Tinkerforge/can-v2-bricklet/software/src/tfcan_mo.c

/* can-v2-bricklet
 * Copyright (C) 2018 Matthias Bolte <matthias@tinkerforge.com>
 *
 * tfcan_mo.c: XMC CAN Message Object helpers
 *
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
 * You should have received a copy of the GNU Lesser General Public
 * License along with this library; if not, write to the
 * Free Software Foundation, Inc., 59 Temple Place - Suite 330,
 * Boston, MA 02111-1307, USA.
 */

#include "tfcan_mo.h"

#include "configs/config.h"
#include "configs/config_tfcan.h"
#include "bricklib2/logging/logging.h"

#include "xmc_can.h"
#include "xmc_can_map.h"

void tfcan_mo_init_tx(CAN_MO_TypeDef *const mo) {
	// reset all status bits
	tfcan_mo_change_status(mo, TFCAN_MO_RESET_STATUS_RX_PENDING |
	                           TFCAN_MO_RESET_STATUS_TX_PENDING |
	                           TFCAN_MO_RESET_STATUS_RX_UPDATING |
	                           TFCAN_MO_RESET_STATUS_NEW_DATA |
	                           TFCAN_MO_RESET_STATUS_MESSAGE_LOST |
	                           TFCAN_MO_RESET_STATUS_MESSAGE_VALID |
	                           TFCAN_MO_RESET_STATUS_RX_TX_SELECTED |
	                           TFCAN_MO_RESET_STATUS_RX_ENABLE |
	                           TFCAN_MO_RESET_STATUS_TX_REQUEST |
	                           TFCAN_MO_RESET_STATUS_TX_ENABLE0 |
	                           TFCAN_MO_RESET_STATUS_TX_ENABLE1 |
	                           TFCAN_MO_RESET_STATUS_DIRECTION);

	// configure MPN and clear all other MOIPR parts
	mo->MOIPR = (((uint32_t)mo - CAN_BASE - 0x1000U) / 0x0020U) << CAN_MO_MOIPR_MPN_Pos;

	// reset all MOFCR parts
	mo->MOFCR = 0;

	// reset all MOFGPR parts
	mo->MOFGPR = 0;

	// reset all MOAMR parts
	mo->MOAMR = 0x3FFFFFFF;

	// clear idenfifier and set priority to 1
	mo->MOAR = 1U << CAN_MO_MOAR_PRI_Pos;

	// clear data
	mo->MODATAL = 0;
	mo->MODATAH = 0;

	// set direction to TX and mark as valid
	tfcan_mo_change_status(mo, TFCAN_MO_SET_STATUS_DIRECTION |
	                           TFCAN_MO_SET_STATUS_MESSAGE_VALID);
}

void tfcan_mo_init_tx_fifo_base(CAN_MO_TypeDef *const mo, const uint8_t base_and_bottom,
                                const uint8_t top) {
	mo->MOFCR = (mo->MOFCR & ~(uint32_t)CAN_MO_MOFCR_MMC_Msk) |
	            (((uint32_t)0x2u << CAN_MO_MOFCR_MMC_Pos) & (uint32_t)CAN_MO_MOFCR_MMC_Msk);

	mo->MOFGPR = (mo->MOFGPR & ~(uint32_t)(CAN_MO_MOFGPR_BOT_Msk |
	                                       CAN_MO_MOFGPR_TOP_Msk |
	                                       CAN_MO_MOFGPR_CUR_Msk)) |
	             (((uint32_t)base_and_bottom << CAN_MO_MOFGPR_CUR_Pos) & (uint32_t)CAN_MO_MOFGPR_CUR_Msk) |
	             (((uint32_t)top << CAN_MO_MOFGPR_TOP_Pos) & (uint32_t)CAN_MO_MOFGPR_TOP_Msk) |
	             (((uint32_t)base_and_bottom << CAN_MO_MOFGPR_BOT_Pos) & (uint32_t)CAN_MO_MOFGPR_BOT_Msk);

	tfcan_mo_change_status(mo, TFCAN_MO_SET_STATUS_TX_ENABLE0 |
	                           TFCAN_MO_SET_STATUS_TX_ENABLE1);
}

void tfcan_mo_init_tx_fifo_slave(CAN_MO_TypeDef *const mo, const uint8_t base) {
	mo->MOFCR = (mo->MOFCR & ~(uint32_t)CAN_MO_MOFCR_MMC_Msk) |
	            (((uint32_t)0x3u << CAN_MO_MOFCR_MMC_Pos) & (uint32_t)CAN_MO_MOFCR_MMC_Msk);

	mo->MOFGPR = (mo->MOFGPR & ~(uint32_t)(CAN_MO_MOFGPR_BOT_Msk |
	                                       CAN_MO_MOFGPR_TOP_Msk |
	                                       CAN_MO_MOFGPR_CUR_Msk)) |
	             (((uint32_t)base << CAN_MO_MOFGPR_CUR_Pos) & (uint32_t)CAN_MO_MOFGPR_CUR_Msk);

	tfcan_mo_change_status(mo, TFCAN_MO_SET_STATUS_TX_ENABLE0 |
	                           TFCAN_MO_RESET_STATUS_TX_ENABLE1);
}

void tfcan_mo_init_rx(CAN_MO_TypeDef *const mo, const TFCAN_BufferType type) {
	// reset all status bits
	tfcan_mo_change_status(mo, TFCAN_MO_RESET_STATUS_RX_PENDING |
	                           TFCAN_MO_RESET_STATUS_TX_PENDING |
	                           TFCAN_MO_RESET_STATUS_RX_UPDATING |
	                           TFCAN_MO_RESET_STATUS_NEW_DATA |
	                           TFCAN_MO_RESET_STATUS_MESSAGE_LOST |
	                           TFCAN_MO_RESET_STATUS_MESSAGE_VALID |
	                           TFCAN_MO_RESET_STATUS_RX_TX_SELECTED |
	                           TFCAN_MO_RESET_STATUS_RX_ENABLE |
	                           TFCAN_MO_RESET_STATUS_TX_REQUEST |
	                           TFCAN_MO_RESET_STATUS_TX_ENABLE0 |
	                           TFCAN_MO_RESET_STATUS_TX_ENABLE1 |
	                           TFCAN_MO_RESET_STATUS_DIRECTION);

	// configure MPN and clear all other MOIPR parts
	mo->MOIPR = (((uint32_t)mo - CAN_BASE - 0x1000u) / 0x0020u) << CAN_MO_MOIPR_MPN_Pos;

	// reset all MOFCR parts
	mo->MOFCR = 0;

	// reset all MOFGPR parts
	mo->MOFGPR = 0;

	// clear all MOAMR parts to accept all messages
	mo->MOAMR = 0;

	// clear idenfifier and set priority to 1
	mo->MOAR = 1u << CAN_MO_MOAR_PRI_Pos;

	// clear data
	mo->MODATAL = 0;
	mo->MODATAH = 0;

	// configure remote frame reception
	if (type == TFCAN_BUFFER_TYPE_REMOTE) {
		tfcan_mo_change_status(mo, TFCAN_MO_SET_STATUS_DIRECTION);
		mo->MOFCR |= (uint32_t)CAN_MO_MOFCR_RMM_Msk;
	}

	// mark as valid
	tfcan_mo_change_status(mo, TFCAN_MO_SET_STATUS_MESSAGE_VALID);
}

void tfcan_mo_init_rx_fifo_base(CAN_MO_TypeDef *const mo, const uint8_t base_and_bottom,
                                const uint8_t top) {
	mo->MOFCR = (mo->MOFCR & ~(uint32_t)CAN_MO_MOFCR_MMC_Msk) |
	            (((uint32_t)0x1u << CAN_MO_MOFCR_MMC_Pos) & (uint32_t)CAN_MO_MOFCR_MMC_Msk);

	mo->MOFGPR = (mo->MOFGPR & ~(uint32_t)(CAN_MO_MOFGPR_BOT_Msk |
	                                       CAN_MO_MOFGPR_TOP_Msk |
	                                       CAN_MO_MOFGPR_CUR_Msk)) |
	             (((uint32_t)base_and_bottom << CAN_MO_MOFGPR_CUR_Pos) & (uint32_t)CAN_MO_MOFGPR_CUR_Msk) |
	             (((uint32_t)top             << CAN_MO_MOFGPR_TOP_Pos) & (uint32_t)CAN_MO_MOFGPR_TOP_Msk) |
	             (((uint32_t)base_and_bottom << CAN_MO_MOFGPR_BOT_Pos) & (uint32_t)CAN_MO_MOFGPR_BOT_Msk);
}

void tfcan_mo_init_rx_fifo_slave(CAN_MO_TypeDef *const mo, const uint8_t base) {
	mo->MOFCR &= ~(uint32_t)CAN_MO_MOFCR_MMC_Msk;

	mo->MOFGPR = (mo->MOFGPR & ~(uint32_t)(CAN_MO_MOFGPR_BOT_Msk |
	                                       CAN_MO_MOFGPR_TOP_Msk |
	                                       CAN_MO_MOFGPR_CUR_Msk)) |
	             (((uint32_t)base << CAN_MO_MOFGPR_CUR_Pos) & (uint32_t)CAN_MO_MOFGPR_CUR_Msk);

	tfcan_mo_change_status(mo, TFCAN_MO_RESET_STATUS_RX_ENABLE);
}

uint32_t tfcan_mo_get_status(const CAN_MO_TypeDef *const mo) {
	return mo->MOCTR;
}

void tfcan_mo_change_status(CAN_MO_TypeDef *const mo, const uint32_t mask) {
	mo->MOCTR = mask;
}

uint16_t tfcan_mo_get_frame_counter(CAN_MO_TypeDef *const mo) {
	return (mo->MOIPR & (uint32_t)CAN_MO_MOIPR_CFCVAL_Msk) >> CAN_MO_MOIPR_CFCVAL_Pos;
}

void tfcan_mo_set_identifier(CAN_MO_TypeDef *const mo, const TFCAN_MOType type,
                             const uint32_t identifier) {
	if (type == TFCAN_MO_TYPE_STANDARD_DATA || type == TFCAN_MO_TYPE_STANDARD_REMOTE) {
		mo->MOAR &= ~(uint32_t)CAN_MO_MOAR_IDE_Msk;
		mo->MOAR = (mo->MOAR & ~(uint32_t)CAN_MO_MOAR_ID_Msk) |
		           ((identifier << 18) & (uint32_t)CAN_MO_MOAR_ID_Msk);
	} else {
		mo->MOAR |= (uint32_t)CAN_MO_MOAR_IDE_Msk;
		mo->MOAR = (mo->MOAR & ~(uint32_t)CAN_MO_MOAR_ID_Msk) |
		           (identifier & (uint32_t)CAN_MO_MOAR_ID_Msk);
	}

	if (type == TFCAN_MO_TYPE_STANDARD_DATA || type == TFCAN_MO_TYPE_EXTENDED_DATA) {
		tfcan_mo_change_status(mo, TFCAN_MO_SET_STATUS_DIRECTION);
	} else {
		tfcan_mo_change_status(mo, TFCAN_MO_RESET_STATUS_DIRECTION);
	}
}

void tfcan_mo_set_data(CAN_MO_TypeDef *const mo, const uint8_t *const data,
                       const uint8_t length) {
	tfcan_mo_change_status(mo, TFCAN_MO_RESET_STATUS_MESSAGE_VALID);

	mo->MOFCR = (mo->MOFCR & ~(uint32_t)CAN_MO_MOFCR_DLC_Msk) |
	            (((uint32_t)length << CAN_MO_MOFCR_DLC_Pos) & CAN_MO_MOFCR_DLC_Msk);

	if ((tfcan_mo_get_status(mo) & TFCAN_MO_STATUS_DIRECTION) != 0) {
		mo->MODATAL = (uint32_t)data[0] | ((uint32_t)data[1] << 8) | ((uint32_t)data[2] << 16) | ((uint32_t)data[3] << 24);
		mo->MODATAH = (uint32_t)data[4] | ((uint32_t)data[5] << 8) | ((uint32_t)data[6] << 16) | ((uint32_t)data[7] << 24);
	} else {
		mo->MODATAL = 0;
		mo->MODATAH = 0;
	}

	tfcan_mo_change_status(mo, TFCAN_MO_RESET_STATUS_RX_TX_SELECTED |
	                           TFCAN_MO_SET_STATUS_MESSAGE_VALID |
	                           TFCAN_MO_SET_STATUS_NEW_DATA);
}

void tfcan_mo_get_identifier(CAN_MO_TypeDef *const mo, TFCAN_MOType *const type,
                             uint32_t *const identifier) {
	if ((((mo->MOAR) & CAN_MO_MOAR_IDE_Msk) >> CAN_MO_MOAR_IDE_Pos) == 0) {
		if ((tfcan_mo_get_status(mo) & TFCAN_MO_STATUS_DIRECTION) == 0) {
			*type = TFCAN_MO_TYPE_STANDARD_DATA;
		} else {
			*type = TFCAN_MO_TYPE_STANDARD_REMOTE;
		}

		*identifier = (mo->MOAR & CAN_MO_MOAR_ID_Msk) >> 18;
	} else {
		if ((tfcan_mo_get_status(mo) & TFCAN_MO_STATUS_DIRECTION) == 0) {
			*type = TFCAN_MO_TYPE_EXTENDED_DATA;
		} else {
			*type = TFCAN_MO_TYPE_EXTENDED_REMOTE;
		}

		*identifier = mo->MOAR & CAN_MO_MOAR_ID_Msk;
	}
}

void tfcan_mo_get_data(CAN_MO_TypeDef *const mo, uint8_t *const data,
                       uint8_t *const length) {
	if ((tfcan_mo_get_status(mo) & TFCAN_MO_STATUS_DIRECTION) == 0) {
		data[0] =  mo->MODATAL        & 0xFF;
		data[1] = (mo->MODATAL >>  8) & 0xFF;
		data[2] = (mo->MODATAL >> 16) & 0xFF;
		data[3] = (mo->MODATAL >> 24) & 0xFF;
		data[4] =  mo->MODATAH        & 0xFF;
		data[5] = (mo->MODATAH >>  8) & 0xFF;
		data[6] = (mo->MODATAH >> 16) & 0xFF;
		data[7] = (mo->MODATAH >> 24) & 0xFF;
	} else {
		memset(data, 0, 8);
	}

	*length = (mo->MOFCR & CAN_MO_MOFCR_DLC_Msk) >> CAN_MO_MOFCR_DLC_Pos;
}

void tfcan_mo_set_tx_fifo_current(CAN_MO_TypeDef *const mo, const uint8_t current) {
	mo->MOFGPR = (mo->MOFGPR & ~(uint32_t)(CAN_MO_MOFGPR_CUR_Msk)) |
	             (((uint32_t)current << CAN_MO_MOFGPR_CUR_Pos) & (uint32_t)CAN_MO_MOFGPR_CUR_Msk);
}

uint8_t tfcan_mo_get_tx_fifo_current(CAN_MO_TypeDef *const mo) {
	return (uint8_t)((uint32_t)(mo->MOFGPR & CAN_MO_MOFGPR_CUR_Msk) >> CAN_MO_MOFGPR_CUR_Pos);
}

void tfcan_mo_set_rx_filter(CAN_MO_TypeDef *const mo, const TFCAN_FilterMode mode,
                            const uint32_t mask, const uint32_t identifier) {
	if (mode == TFCAN_FILTER_MODE_ACCEPT_ALL) {
		mo->MOAMR = 0;
		mo->MOAR &= ~((uint32_t)CAN_MO_MOAR_IDE_Msk | (uint32_t)CAN_MO_MOAR_ID_Msk);
	} else if (mode == TFCAN_FILTER_MODE_MATCH_STANDARD_ONLY) {
		mo->MOAMR = (uint32_t)CAN_MO_MOAMR_MIDE_Msk | ((mask << 18) & (uint32_t)CAN_MO_MOAMR_AM_Msk);
		mo->MOAR = (mo->MOAR & ~((uint32_t)CAN_MO_MOAR_ID_Msk | (uint32_t)CAN_MO_MOAR_IDE_Msk)) |
		           ((identifier << 18) & (uint32_t)CAN_MO_MOAR_ID_Msk);
	} else if (mode == TFCAN_FILTER_MODE_MATCH_EXTENDED_ONLY) {
		mo->MOAMR = (uint32_t)CAN_MO_MOAMR_MIDE_Msk | (mask & (uint32_t)CAN_MO_MOAMR_AM_Msk);
		mo->MOAR = (mo->MOAR & ~(uint32_t)CAN_MO_MOAR_ID_Msk) |
		           (uint32_t)CAN_MO_MOAR_IDE_Msk | (identifier & CAN_MO_MOAR_ID_Msk);
	} else if (mode == TFCAN_FILTER_MODE_MATCH_STANDARD_AND_EXTENDED) {
		mo->MOAMR = mask & (uint32_t)CAN_MO_MOAMR_AM_Msk;
		mo->MOAR = (mo->MOAR & ~(uint32_t)CAN_MO_MOAR_ID_Msk) |
		           (uint32_t)CAN_MO_MOAR_IDE_Msk | (identifier & (uint32_t)CAN_MO_MOAR_ID_Msk);
	}
}
